mmaharebi/MicrowaveWaveguideAntennaDesign/imgs/exp3_dBS11_ads.png

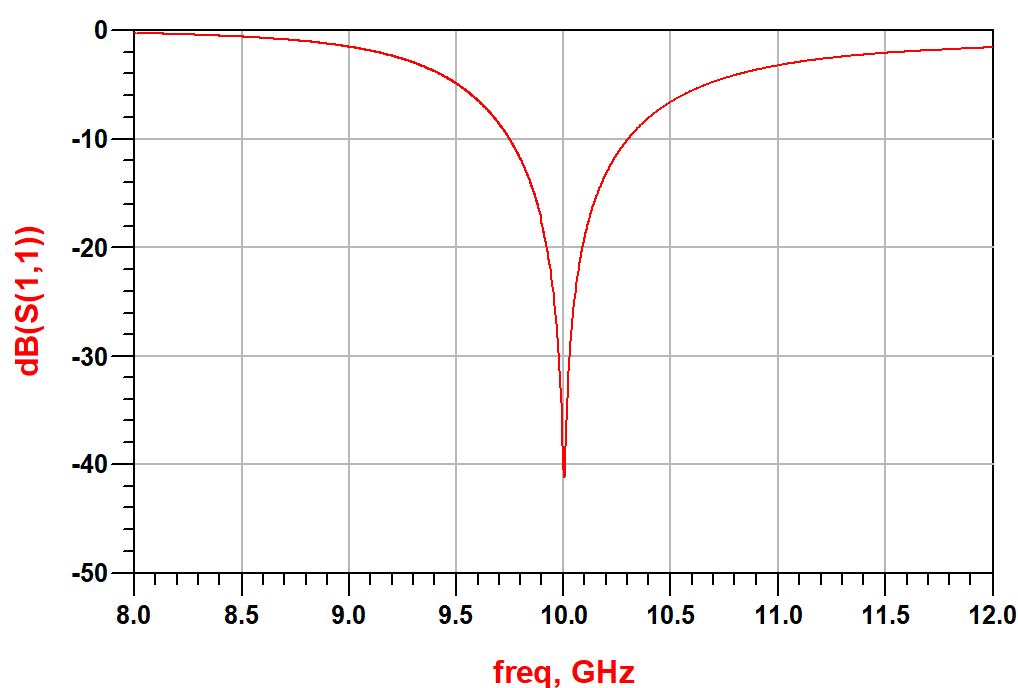
imgs/exp3_dBS11_ads.png
