mmaharebi/MicrowaveWaveguideAntennaDesign/Project1 - Dimensions.PNG

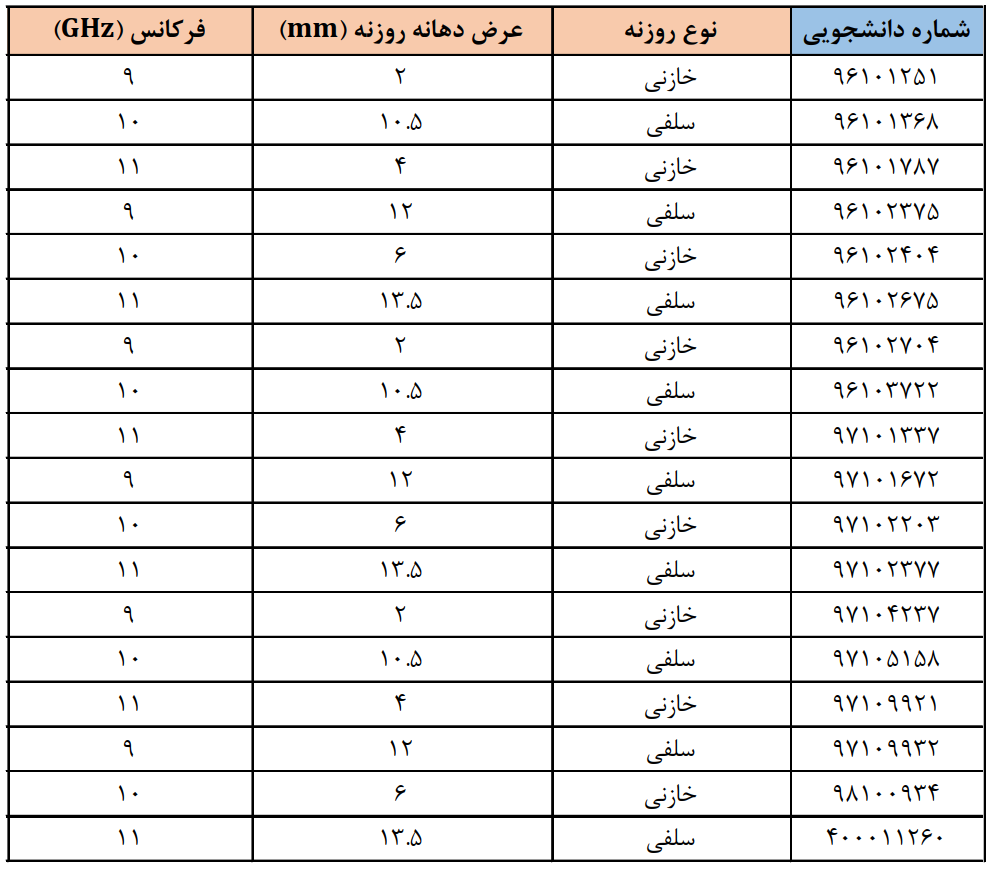
Project1 - Dimensions.PNG
